europer/Logitech-G29-Load-Cell/img/IMG_20201223_135305.jpg

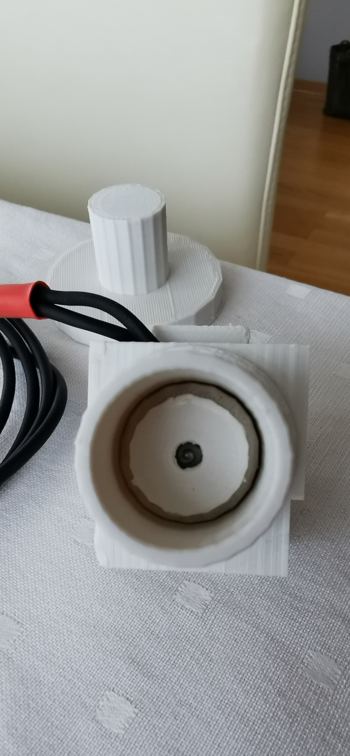
img/IMG_20201223_135305.jpg
